blackmountainb/RespiratoryFrequencyMeasurer/Images/p1.jpeg

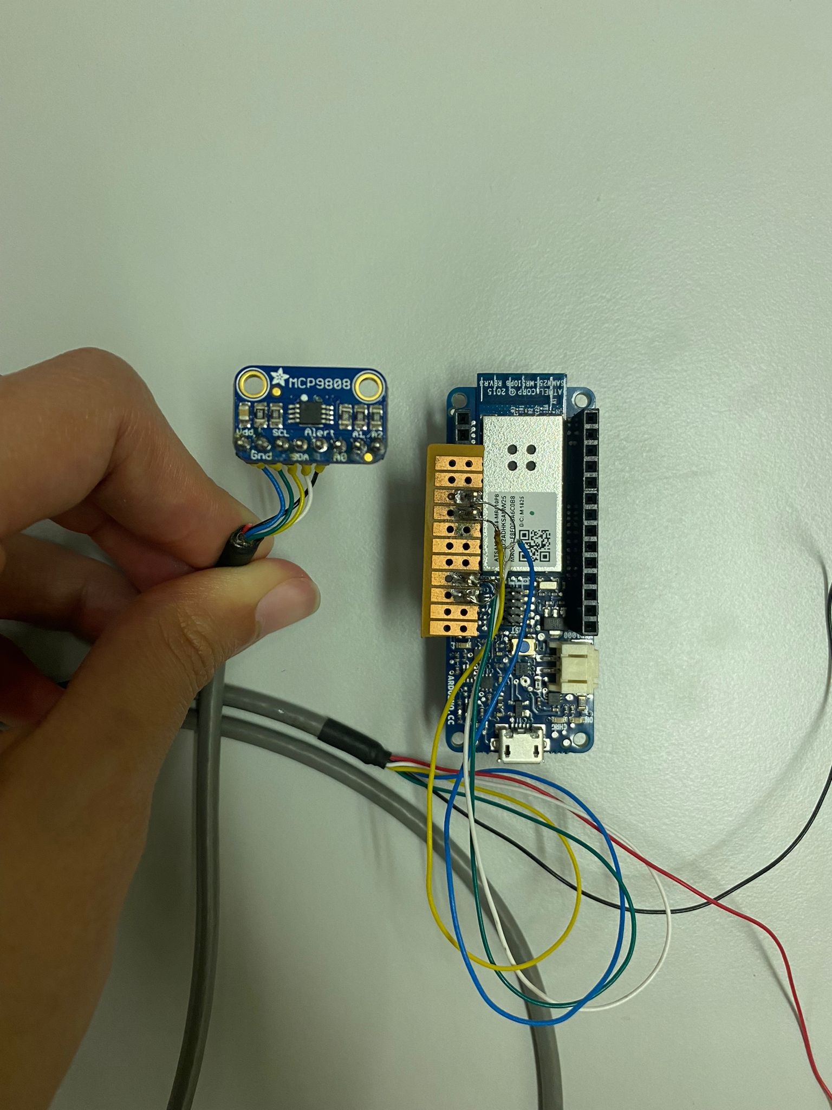
Images/p1.jpeg
