blackmountainb/RespiratoryFrequencyMeasurer/Images/p2.jpeg

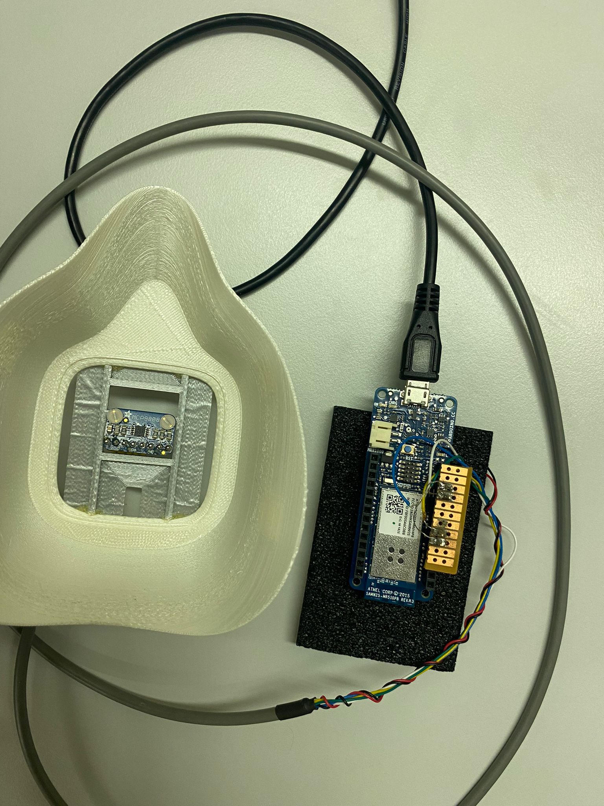
Images/p2.jpeg
