blackmountainb/RespiratoryFrequencyMeasurer/Images/p3.jpeg

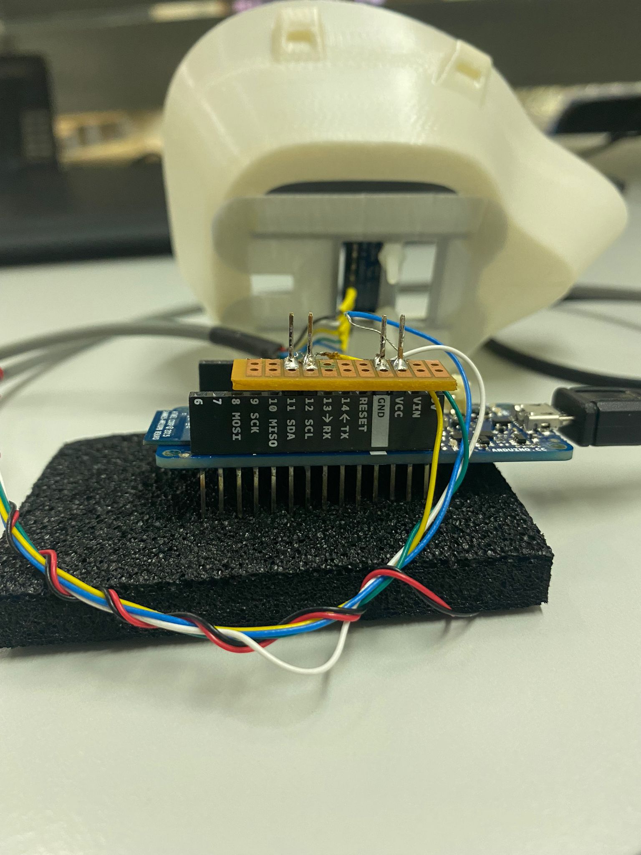
Images/p3.jpeg
