blackmountainb/RespiratoryFrequencyMeasurer/Images/p4.jpeg

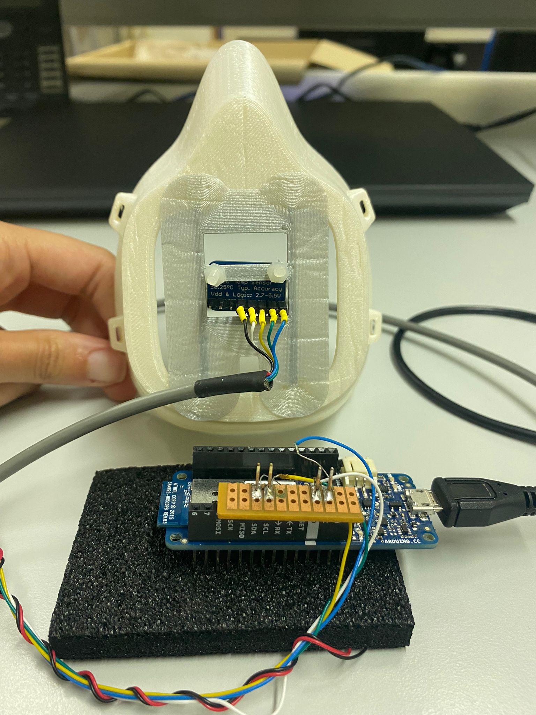
Images/p4.jpeg
